AIFanatic/PaperLedger/firmware/src/icons.h

#ifndef _ICONS_H_
#define _ICONS_H_

#include <pgmspace.h>

const unsigned char ICON_LEFT_ARROW_64[] PROGMEM = {
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
};

const unsigned char ICON_BOLT_16[] PROGMEM = {
    0x01,0xE0,0x03,0xE0,0x03,0xC0,0x03,0xC0,0x07,0x80,0x07,0xF0,0x0F,0xE0,0x0F,0xC0,0x01,0xC0,0x01,0x80,0x03,0x00,0x03,0x00,0x06,0x00,0x04,0x00,0x04,0x00,0x00,0x00
};

const unsigned char ICON_SLEEP_16[] PROGMEM = {
    0x00,0x00,0x10,0xFC,0x30,0xFC,0x70,0x1C,0x70,0x38,0xF0,0x70,0xF0,0xFC,0xF8,0xFC,0xF8,0x00,0xFC,0x00,0xFE,0x00,0x7F,0x80,0x7F,0xFE,0x3F,0xFC,0x1F,0xF8,0x07,0xE0
};

const unsigned char ICON_BAT_16[] PROGMEM = {
    0x00,0x00,0x28,0x00,0x28,0x00,0x7C,0x00,0x45,0xFE,0x44,0x02,0x6D,0xFA,0x39,0xFB,0x13,0xFB,0x17,0xFA,0x10,0x02,0x17,0xFE,0x00,0x00,0x00,0x00,0x00,0x00,0x00,0x00
};

const unsigned char* const ICONS[] PROGMEM = {
    ICON_LEFT_ARROW_64,
    ICON_RIGHT_ARROW_64,
    ICON_UP_ARROW_64,
    ICON_DOWN_ARROW_64,
    ICON_SETTINGS_64,
    ICON_WALLET_64,
    ICON_CHART_64,
    ICON_BOLT_16,
    ICON_SLEEP_16,
    ICON_BAT_16
};

#endif
