AIFanatic/PaperLedger/firmware/src/app/controller/DeepSleep.h

#ifndef DeepSleep_h
#define DeepSleep_h

#include <Arduino.h>

class Manager;

class DeepSleep {
    public:
        DeepSleep(Manager *_manager);
        ~DeepSleep(void);

        int getWakeupCause();

        bool hasBootedFromDeepSleep();

        bool canEnterDeepSleep();
        void enterDeepSleep();
        bool isGoingToDeepSleep();

        void setMinAwakeBootTimeOffset(long offsetMillis);

        void update();

    private:
        Manager *manager;

        long minAwakeBootTime = 0;
        bool needDeepSleep = false;
        int sleepCountdown = 1000;

        bool deepSleepEnabled = true;
};

#endif
