AIFanatic/PaperLedger/src/LayoutWifi.h

#ifndef LAYOUTWIFI_H
#define LAYOUTWIFI_H

#include <Render.h>
#include <Display.h>
#include <LayoutBase.h>
#include <MenuBackend.h>
#include <LayoutList.h>

class LayoutWifi: public LayoutBase {
    public:
        LayoutWifi(Render *render, Display *_display);
        ~LayoutWifi(void);

    private:
        void initMenu();
        void showMenu();

        void leftButtonClicked();
        void rightButtonClicked();
        void okButtonClicked();

        static void menuChangeEventStatic(MenuChangeEvent changed, void *context);
        void menuChangeEvent(MenuChangeEvent changed);

        LayoutList *menuList;

        MenuBackend *menuRoot;

        MenuItem wifi_status = MenuItem("Wifi_Status");
        MenuItem wifi_connect = MenuItem("Wifi_Connect");
        MenuItem wifi_disconnect = MenuItem("Wifi_Disconnect");
        MenuItem wifi_back = MenuItem("Wifi_Back");
        MenuItem wifi_back_pressed = MenuItem("Wifi_Back_Pressed");
};

#endif
